JarrenLange/TeslaMidiMultiToneController/Tester/Schematic/Tester.kicad_sch

## KiCad design Tester/Schematic/Tester.kicad_sch (2023-10-28)

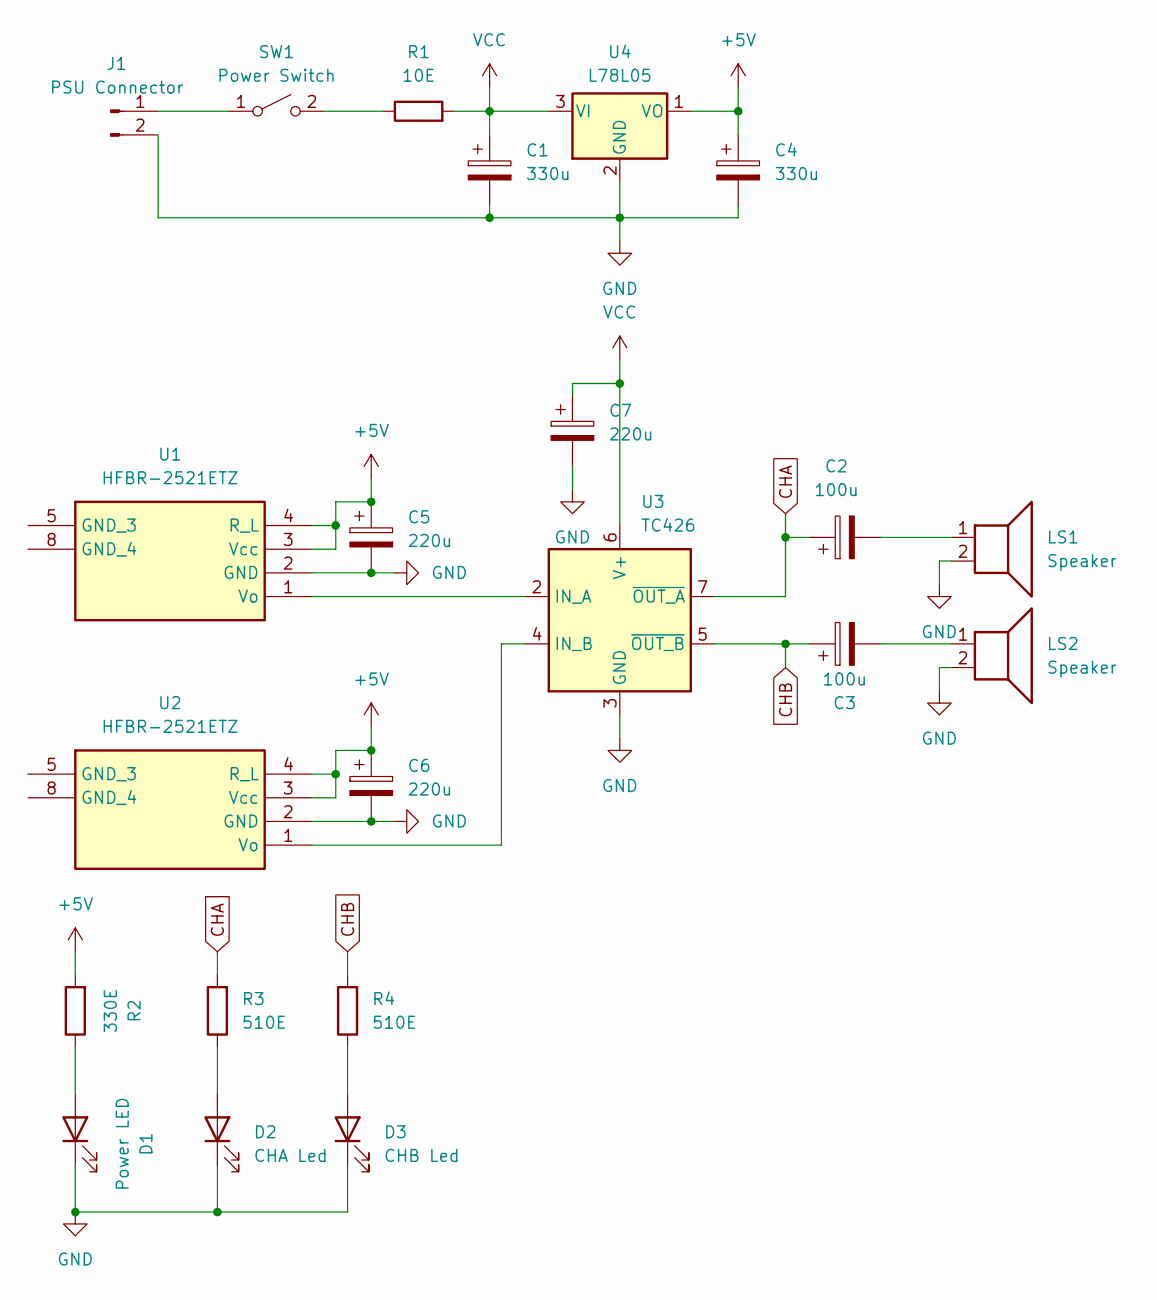
[picture p3: schematic Tester.kicad_sch]

Parts:
C1, C4: 330u
C2, C3: 100u
C5, C6, C7: 220u
D1: Power LED
D2: CHA Led
D3: CHB Led
J1: PSU Connector
LS1, LS2: Speaker
R1: 10E
R2: 330E
R3, R4: 510E
SW1: Power Switch
U1, U2: HFBR-2521ETZ; HFBR2521ETZ; Mouser Part Number 630-HFBR-2521ETZ
U3: TC426
U4: L78L05; TO-92_Inline

Connections:
+5V: C4.1, C5.1, C6.1, R2.2, U1.3 (Vcc), U1.4 (R_L), U2.3 (Vcc), U2.4 (R_L), U4.1 (VO)
CHA: C2.1, R3.2, U3.7 (~OUT_A)
CHB: C3.1, R4.2, U3.5 (~OUT_B)
GND: C1.2, C4.2, C5.2, C6.2, C7.2, D1.1 (K), D2.1 (K), D3.1 (K), J1.2, LS1.2, LS2.2, U1.2 (GND), U2.2 (GND), U3.3 (GND), U4.2 (GND)
unnamed: C2.2, LS1.1
unnamed: C3.2, LS2.1
unnamed: D1.2 (A), R2.1
unnamed: D2.2 (A), R3.1
unnamed: D3.2 (A), R4.1
unnamed: J1.1, SW1.1 (A)
unnamed: R1.1, SW1.2 (B)
unnamed: U1.1 (Vo), U3.2 (IN_A)
unnamed: U2.1 (Vo), U3.4 (IN_B)
VCC: C1.1, C7.1, R1.2, U3.6 (V+), U4.3 (VI)
