JarrenLange/TeslaMidiMultiToneController/Schematic/TeslaCoilControllerSchematic/FibreOpticInterface.kicad_sch

## KiCad design Schematic/TeslaCoilControllerSchematic/FibreOpticInterface.kicad_sch (2023-10-27)

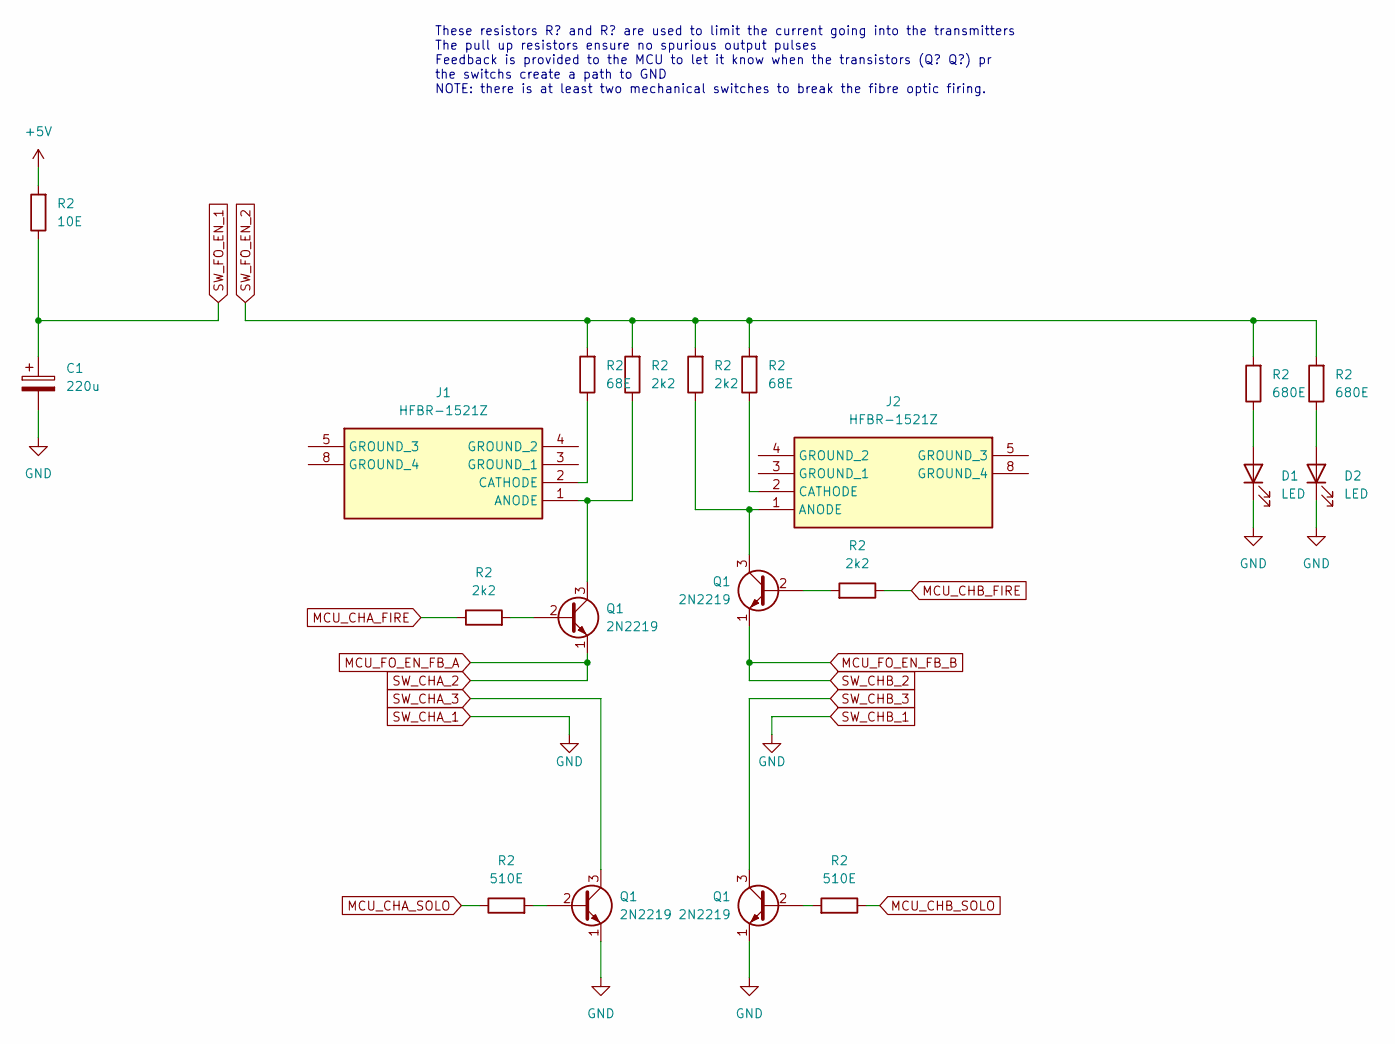
[picture p4: schematic FibreOpticInterface.kicad_sch]

Parts:
C1: 220u
D1, D2: LED
J1, J2: HFBR-1521Z; HFBR1521Z; Mouser Part Number 630-HFBR-1521Z
Q1: 2N2219; TO-39-3
R2: 2k2

Connections:
+5V: R2.2
GND: C1.2, D1.1 (K), D2.1 (K), Q1.1 (E)
MCU_CHA_FIRE: R2.1
MCU_CHA_SOLO: R2.1
MCU_CHB_FIRE: R2.1
MCU_CHB_SOLO: R2.1
MCU_FO_EN_FB_A: Q1.1 (E)
MCU_FO_EN_FB_B: Q1.1 (E)
unnamed: D1.2 (A), R2.1
unnamed: D2.2 (A), R2.1
unnamed: J1.1 (ANODE), Q1.3 (C), R2.1
unnamed: J1.2 (CATHODE), R2.1
unnamed: J2.1 (ANODE), Q1.3 (C), R2.1
unnamed: J2.2 (CATHODE), R2.1
unnamed: Q1.2 (B), R2.2
SW_CHA_3: Q1.3 (C)
SW_CHB_3: Q1.3 (C)
SW_FO_EN_1: C1.1, R2.1
SW_FO_EN_2: R2.2

Notes on the sheet:
These resistors R? and R? are used to limit the current going into the transmitters The pull up resistors ensure no spurious output pulses Feedback is provided to the MCU to let it know when the transistors (Q? Q?) pr the switchs create a path to GND NOTE: there is at least two mechanical switches 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
