JarrenLange/TeslaMidiMultiToneController/Schematic/TeslaCoilControllerSchematic/LCDInterface.kicad_sch

## KiCad design Schematic/TeslaCoilControllerSchematic/LCDInterface.kicad_sch (2023-10-27)

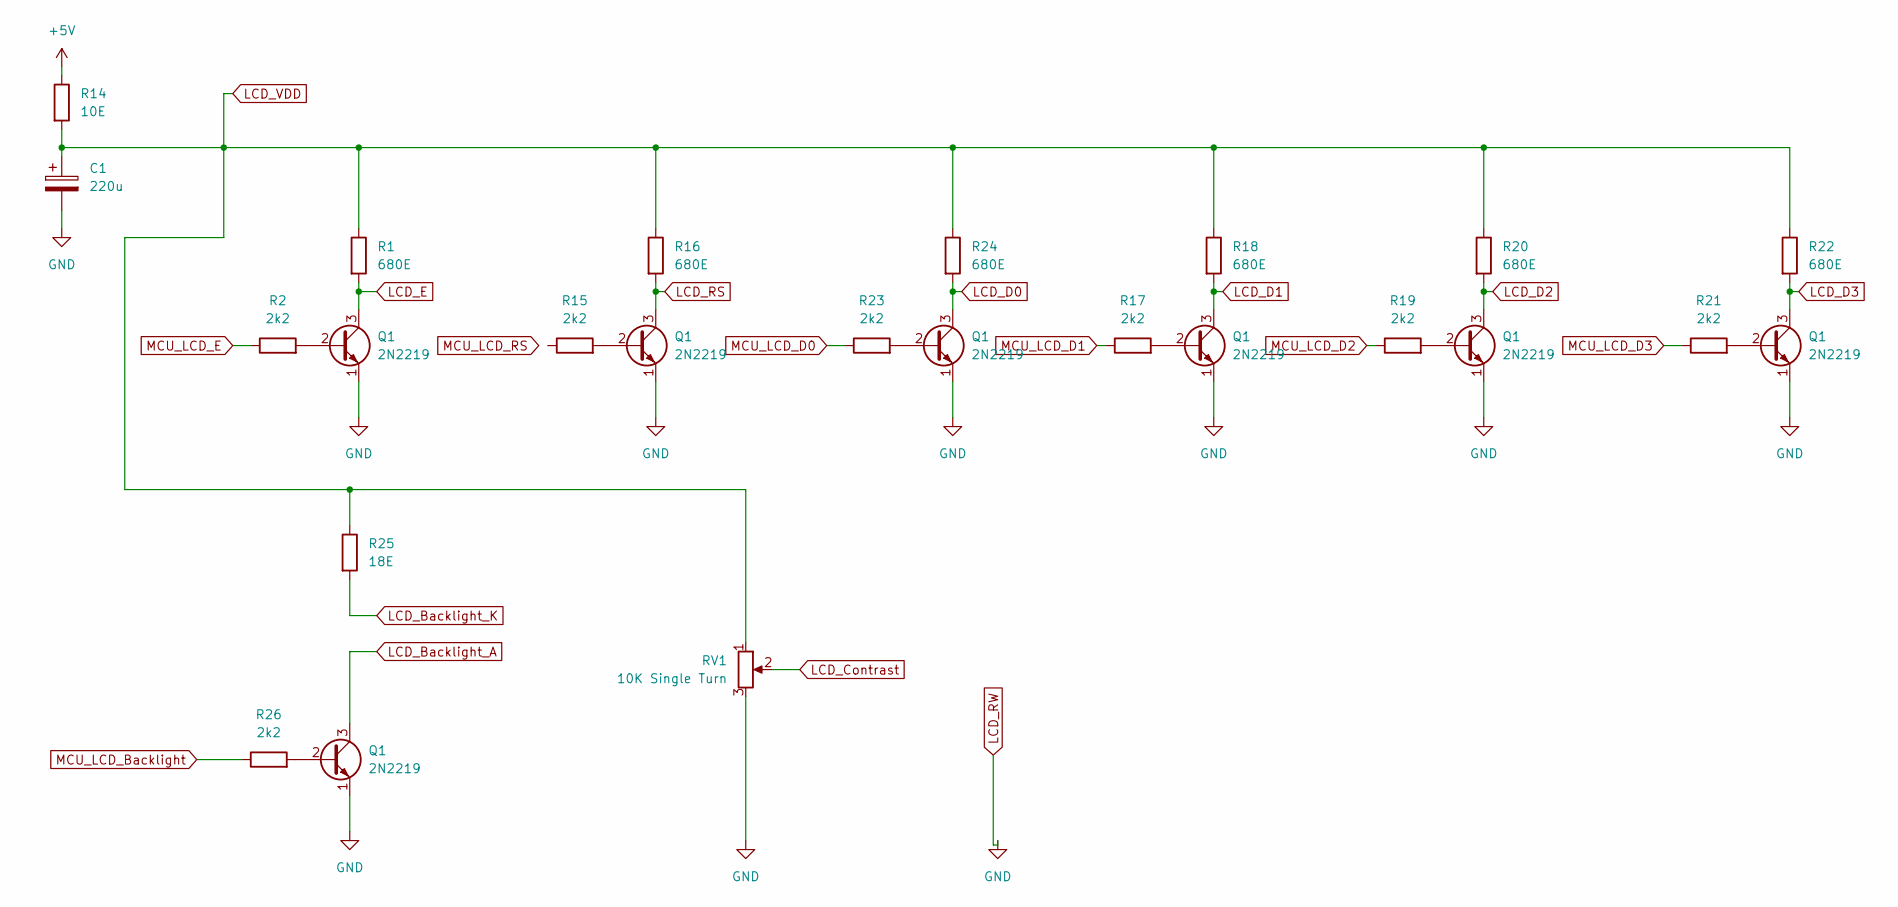
[picture p5: schematic LCDInterface.kicad_sch]

Parts:
C1: 220u
Q1: 2N2219; TO-39-3
R1, R16, R18, R20, R22, R24: 680E
R2, R15, R17, R19, R21, R23, R26: 2k2
R14: 10E
R25: 18E
RV1: 10K Single Turn

Connections:
+5V: R14.1
GND: C1.2, Q1.1 (E), RV1.3
LCD_Backlight_A: Q1.3 (C)
LCD_Backlight_K: R25.2
LCD_Contrast: RV1.2
LCD_D0: Q1.3 (C), R24.2
LCD_D1: Q1.3 (C), R18.2
LCD_D2: Q1.3 (C), R20.2
LCD_D3: Q1.3 (C), R22.2
LCD_E: Q1.3 (C), R1.2
LCD_RS: Q1.3 (C), R16.2
LCD_VDD: C1.1, R1.1, R14.2, R16.1, R18.1, R20.1, R22.1, R24.1, R25.1, RV1.1
MCU_LCD_Backlight: R26.1
MCU_LCD_D0: R23.1
MCU_LCD_D1: R17.1
MCU_LCD_D2: R19.1
MCU_LCD_D3: R21.1
MCU_LCD_E: R2.1
unnamed: Q1.2 (B), R2.2, R15.2, R17.2, R19.2, R21.2, R23.2, R26.2
