JarrenLange/TeslaMidiMultiToneController/Schematic/TeslaCoilControllerSchematic/RibbonAccessories.kicad_sch

## KiCad design Schematic/TeslaCoilControllerSchematic/RibbonAccessories.kicad_sch (2023-10-27)

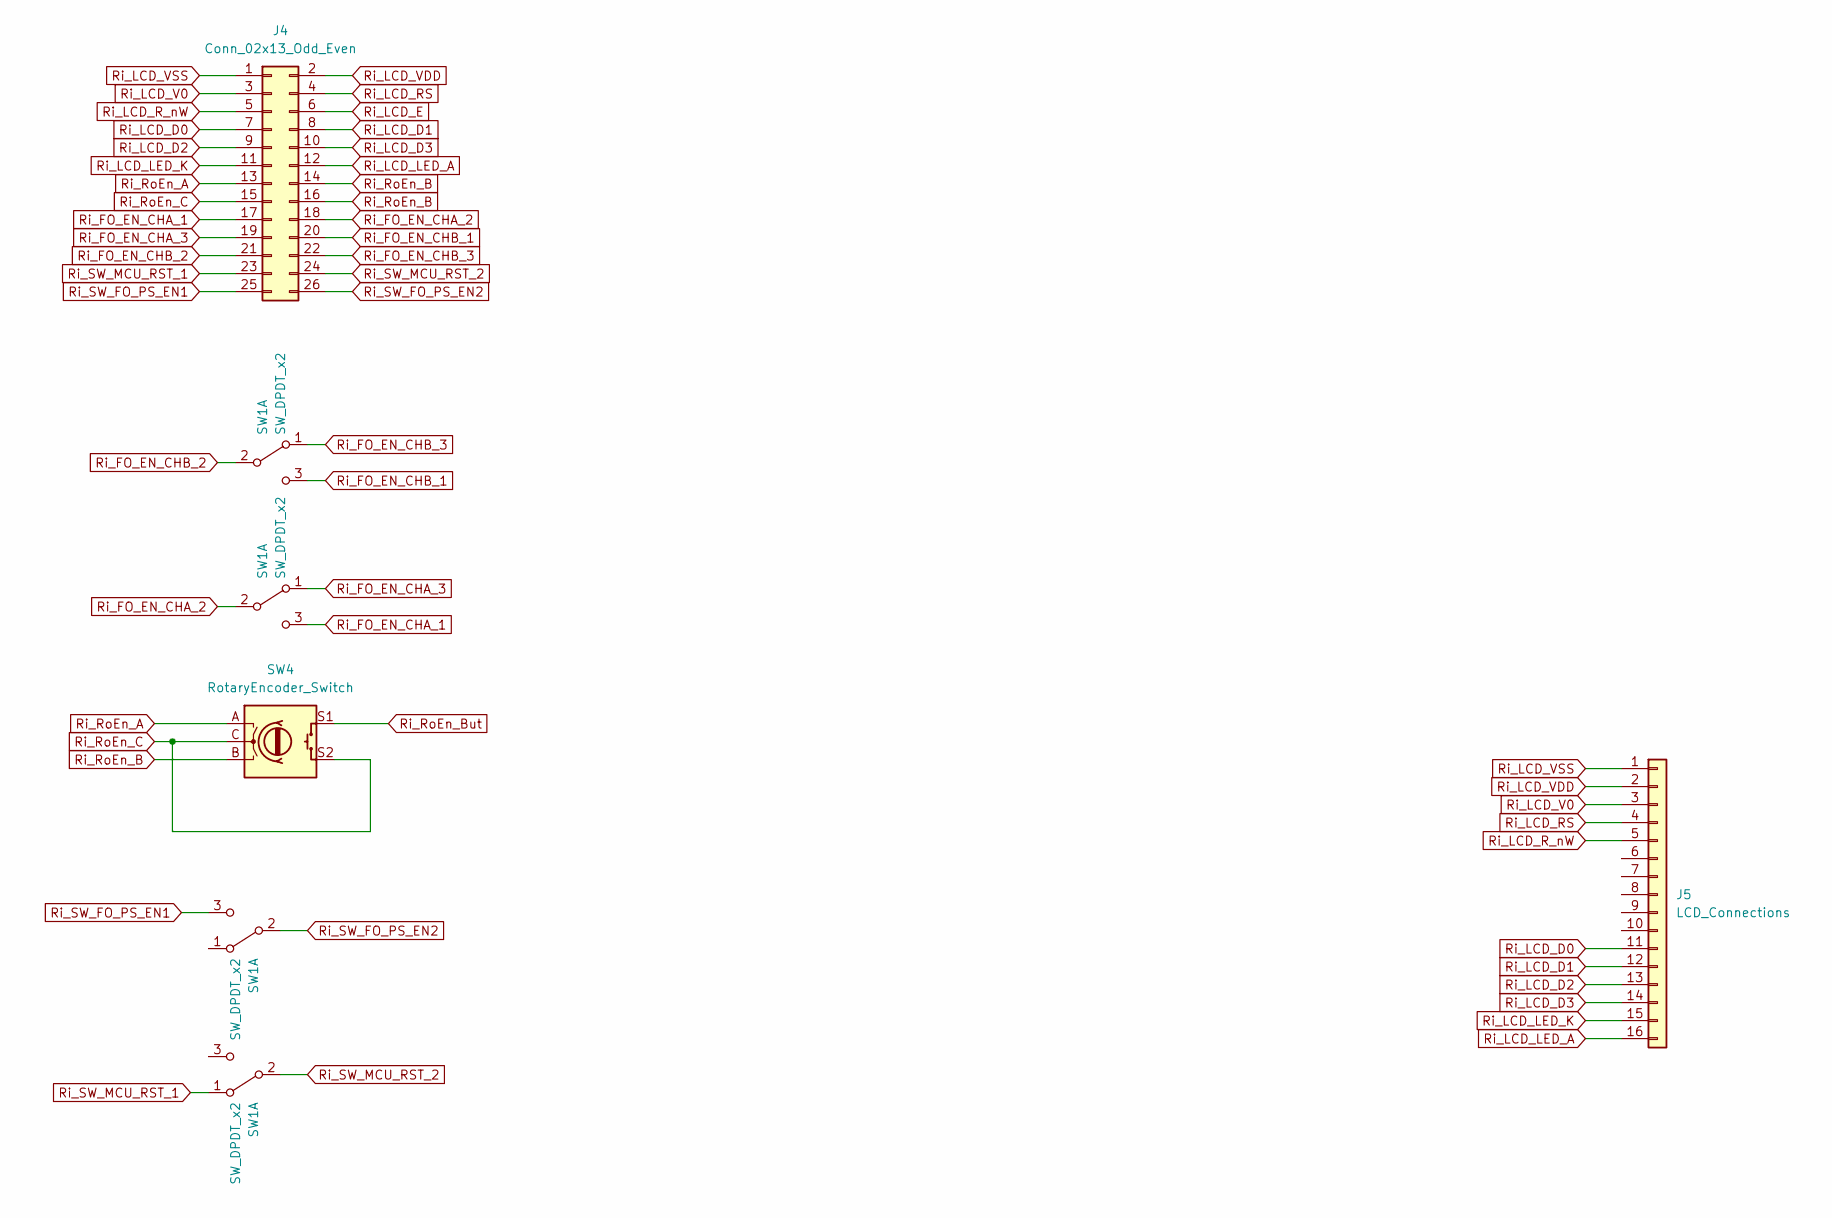
[picture p6: schematic RibbonAccessories.kicad_sch]

Parts:
J4: Conn_02x13_Odd_Even
J5: LCD_Connections
SW1: SW_DPDT_x2
SW4: RotaryEncoder_Switch

Connections:
Ri_FO_EN_CHA_1: J4.17, SW1.3 (C)
Ri_FO_EN_CHA_2: J4.18, SW1.2 (B)
Ri_FO_EN_CHA_3: J4.19, SW1.1 (A)
Ri_FO_EN_CHB_1: J4.20, SW1.3 (C)
Ri_FO_EN_CHB_2: J4.21, SW1.2 (B)
Ri_FO_EN_CHB_3: J4.22, SW1.1 (A)
Ri_LCD_D0: J4.7, J5.11
Ri_LCD_D1: J4.8, J5.12
Ri_LCD_D2: J4.9, J5.13
Ri_LCD_D3: J4.10, J5.14
Ri_LCD_E: J4.6
Ri_LCD_LED_A: J4.12, J5.16
Ri_LCD_LED_K: J4.11, J5.15
Ri_LCD_RS: J4.4, J5.4
Ri_LCD_R_nW: J4.5, J5.5
Ri_LCD_V0: J4.3, J5.3
Ri_LCD_VDD: J4.2, J5.2
Ri_LCD_VSS: J4.1, J5.1
Ri_RoEn_A: J4.13, SW4.A
Ri_RoEn_B: J4.14, J4.16, SW4.B
Ri_RoEn_But: SW4.S1
Ri_RoEn_C: J4.15, SW4.C, SW4.S2
Ri_SW_FO_PS_EN1: J4.25, SW1.3 (C)
Ri_SW_FO_PS_EN2: J4.26, SW1.2 (B)
Ri_SW_MCU_RST_1: J4.23, SW1.1 (A)
Ri_SW_MCU_RST_2: J4.24, SW1.2 (B)
