JarrenLange/TeslaMidiMultiToneController/Schematic/TeslaCoilControllerSchematic/TeslaCoilControllerSchematic.kicad_sch

## KiCad design Schematic/TeslaCoilControllerSchematic/TeslaCoilControllerSchematic.kicad_sch (2023-10-27)

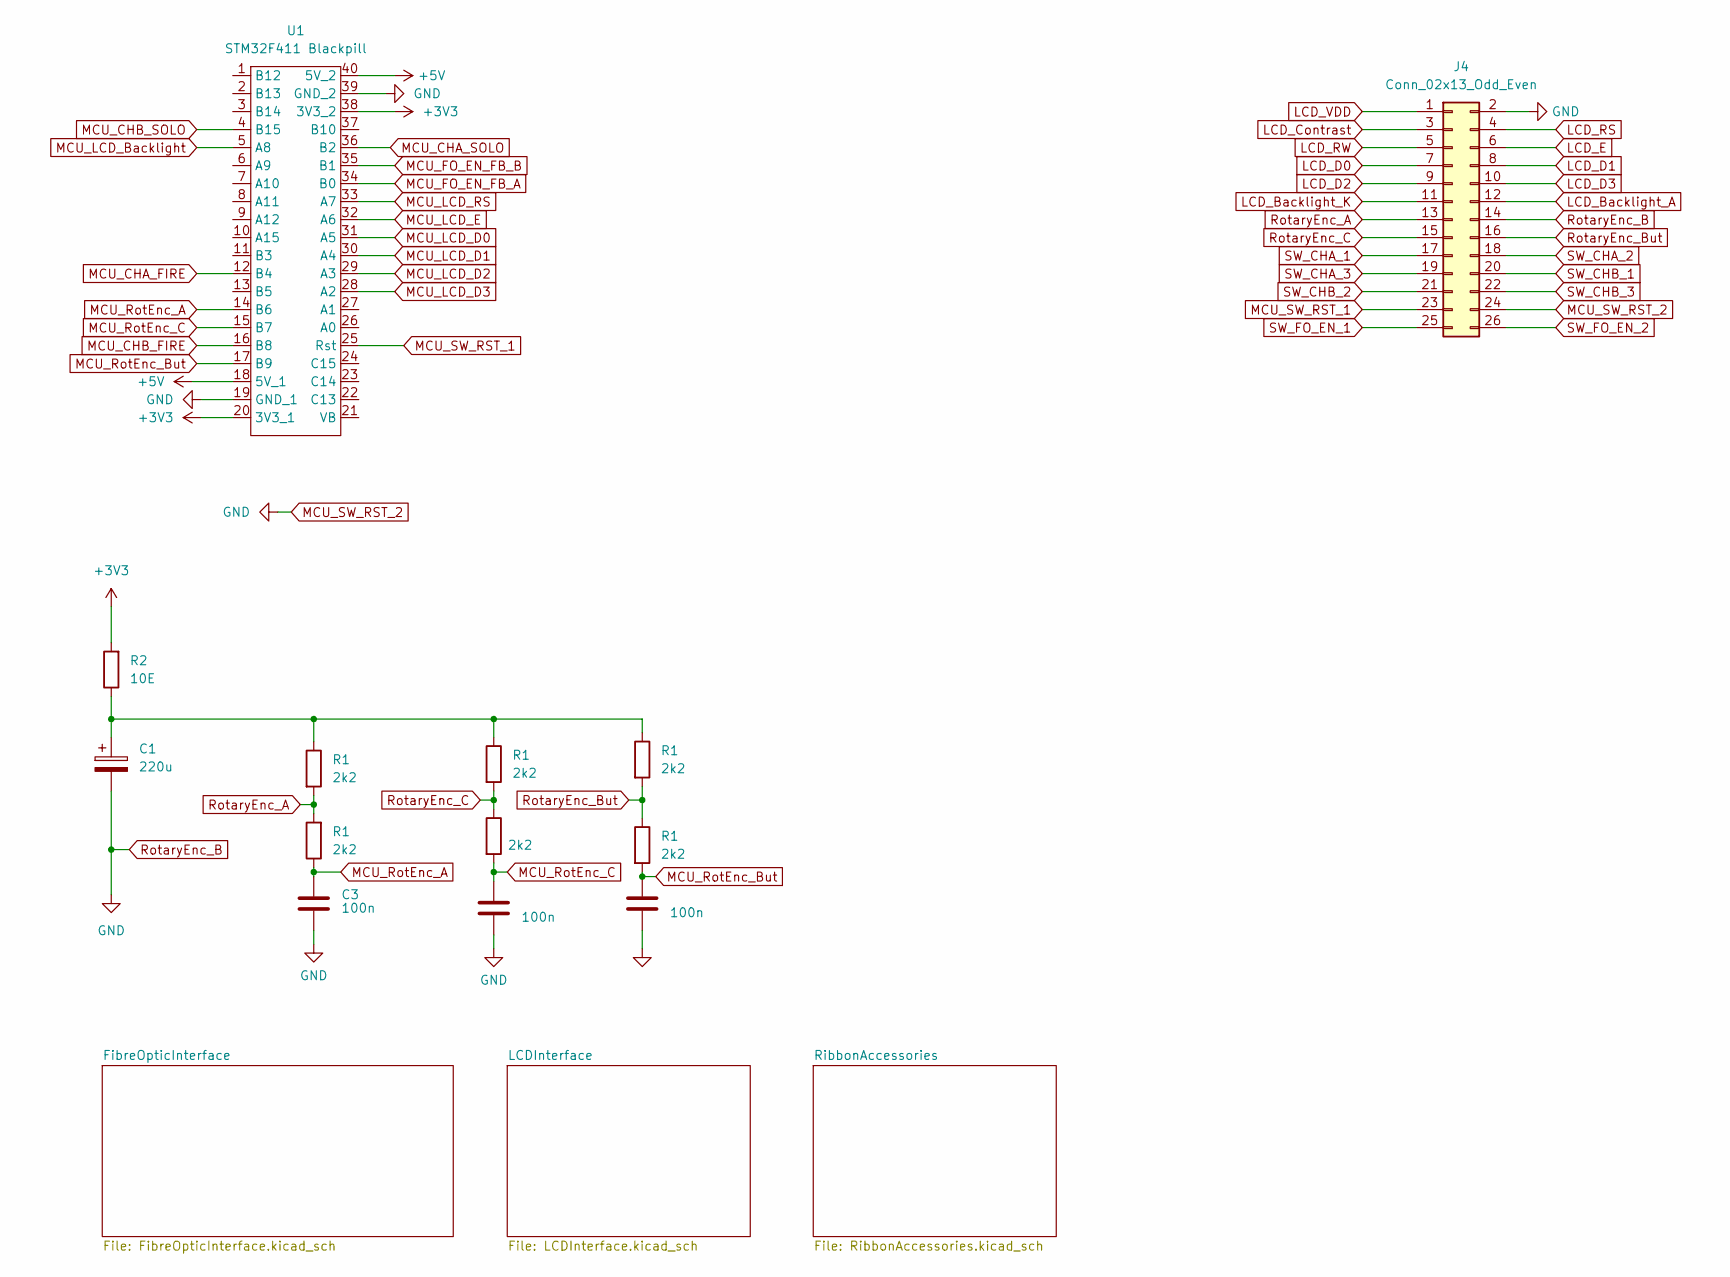
[picture p7: schematic TeslaCoilControllerSchematic.kicad_sch]

Parts:
C1: 220u
C3, C5, C6: 100n
J4: Conn_02x13_Odd_Even
R1: 2k2
R2: 10E
U1: STM32F411 Blackpill

Connections:
+3V3: R2.2, U1.20 (3V3_1), U1.38 (3V3_2)
+5V: U1.18 (5V_1), U1.40 (5V_2)
GND: C1.2, C3.2, C5.2, C6.2, J4.2, J4.14, J4.24, U1.19 (GND_1), U1.39 (GND_2)
LCD_Backlight_A: J4.12
LCD_Backlight_K: J4.11
LCD_Contrast: J4.3
LCD_D0: J4.7
LCD_D1: J4.8
LCD_D2: J4.9
LCD_D3: J4.10
LCD_E: J4.6
LCD_RS: J4.4
LCD_RW: J4.5
LCD_VDD: J4.1
MCU_CHA_FIRE: U1.12 (B4)
MCU_CHA_SOLO: U1.36 (B2)
MCU_CHB_FIRE: U1.16 (B8)
MCU_CHB_SOLO: U1.4 (B15)
MCU_FO_EN_FB_A: U1.34 (B0)
MCU_FO_EN_FB_B: U1.35 (B1)
MCU_LCD_Backlight: U1.5 (A8)
MCU_LCD_D0: U1.31 (A5)
MCU_LCD_D1: U1.30 (A4)
MCU_LCD_D2: U1.29 (A3)
MCU_LCD_D3: U1.28 (A2)
MCU_LCD_E: U1.32 (A6)
MCU_LCD_RS: U1.33 (A7)
MCU_RotEnc_A: C3.1, R1.1, U1.14 (B6)
MCU_RotEnc_But: C6.1, R1.2, U1.17 (B9)
MCU_RotEnc_C: C5.1, R1.2, U1.15 (B7)
MCU_SW_RST_1: J4.23, U1.25 (Rst)
unnamed: C1.1, R1.1, R2.1
RotaryEnc_A: J4.13, R1.2
RotaryEnc_But: J4.16, R1.1, R1.2
RotaryEnc_C: J4.15, R1.1, R1.2
SW_CHA_1: J4.17
SW_CHA_2: J4.18
SW_CHA_3: J4.19
SW_CHB_1: J4.20
SW_CHB_2: J4.21
SW_CHB_3: J4.22
SW_FO_EN_1: J4.25
SW_FO_EN_2: J4.26
