JarrenLange/TeslaMidiMultiToneController/Code/TeslaMidiInterupter/Core/Inc/Pinouts.h

/*
 * Pinouts.h
 *
 *  Created on: 21 Aug 2022
 *      Author: Jarren Lange
 */

#ifndef INC_PINOUTS_H_
#define INC_PINOUTS_H_

/*
//PA0 not 5V tolerant
#define LCD_RS A7
#define LCD_E A6

ENC_BTN B9
ENC_A   B6
ENC_B	B7

*/

#endif /* INC_PINOUTS_H_ */
